AlejoBSmith/VentiladorMecanico/Imágenes/1_isometrico.PNG

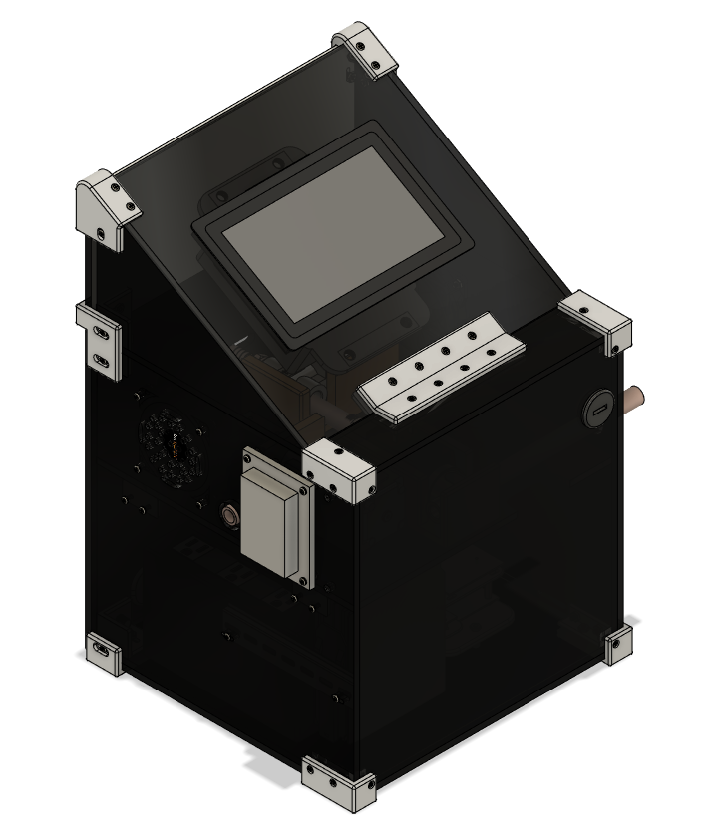
Imágenes/1_isometrico.PNG
