AlejoBSmith/VentiladorMecanico/Imágenes/4_isometrico.PNG

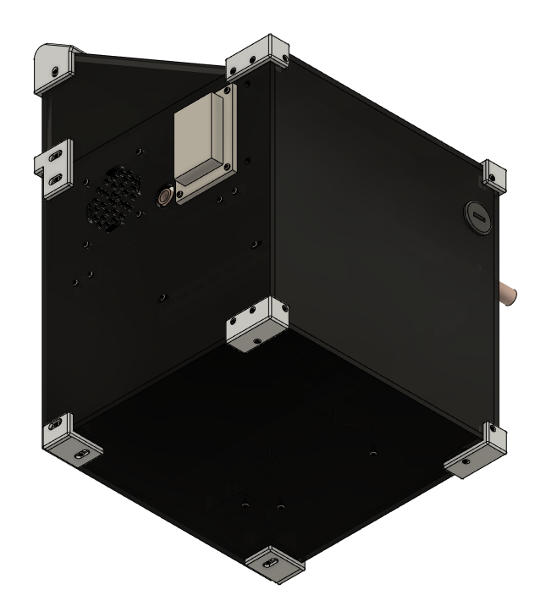
Imágenes/4_isometrico.PNG
