AlejoBSmith/VentiladorMecanico/Imágenes/5_isometrico.PNG

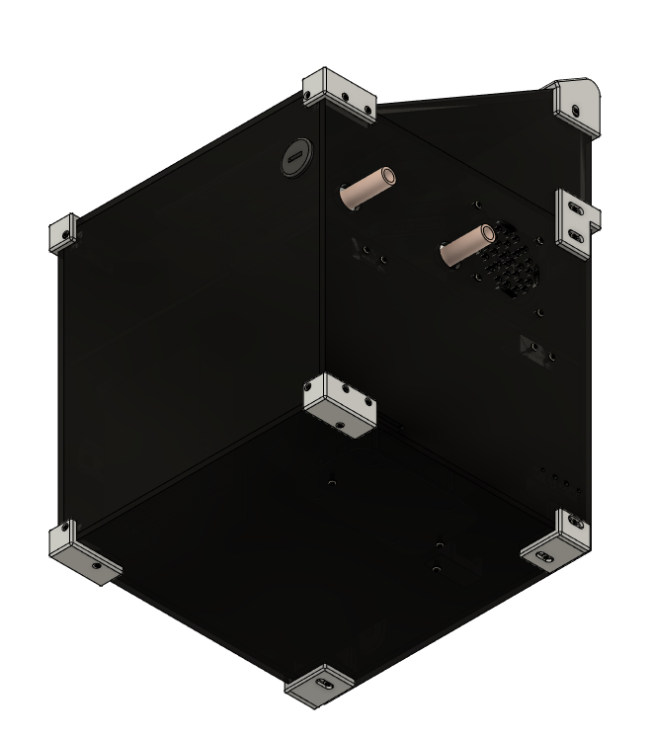
Imágenes/5_isometrico.PNG
