AlejoBSmith/VentiladorMecanico/Imágenes/7_isometrico.PNG

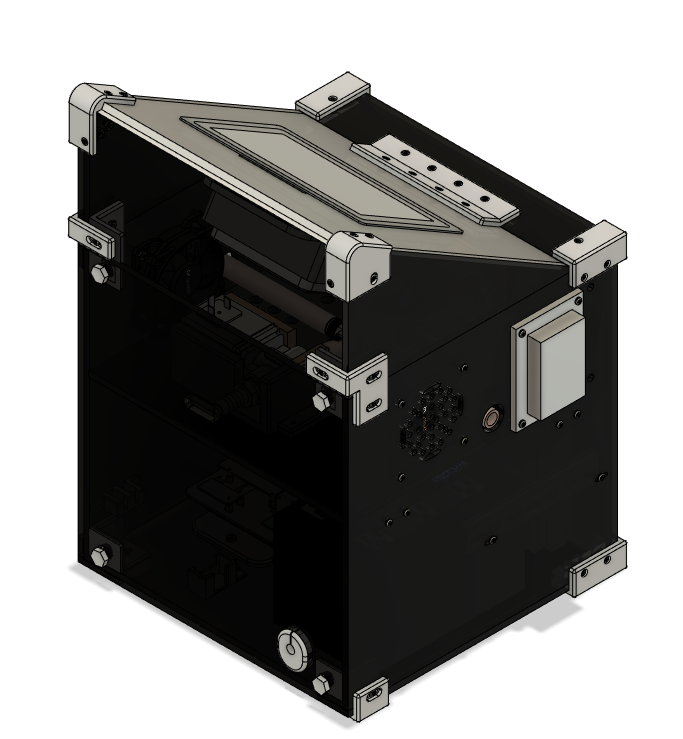
Imágenes/7_isometrico.PNG
