AlejoBSmith/VentiladorMecanico/Imágenes/8_isometrico.PNG

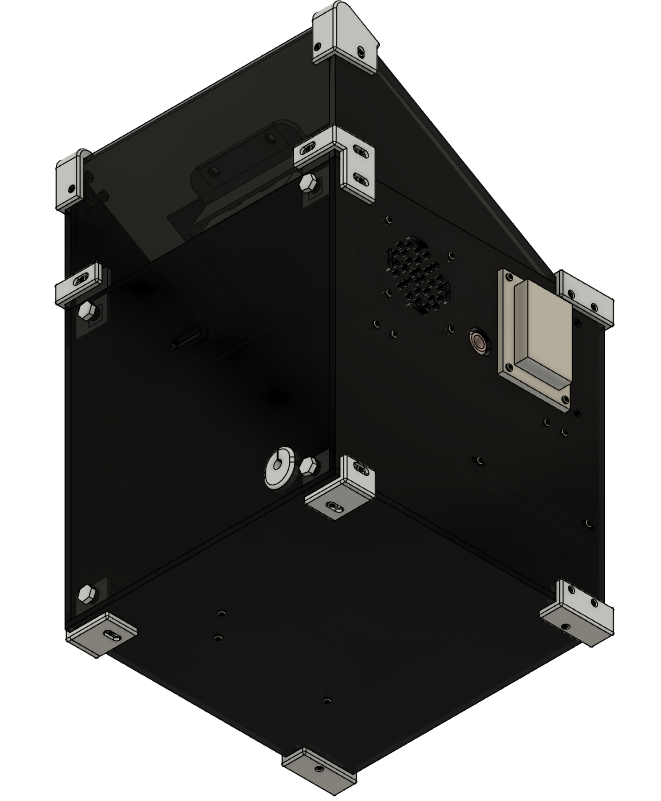
Imágenes/8_isometrico.PNG
