AlejoBSmith/VentiladorMecanico/Imágenes/9_isometrico.PNG

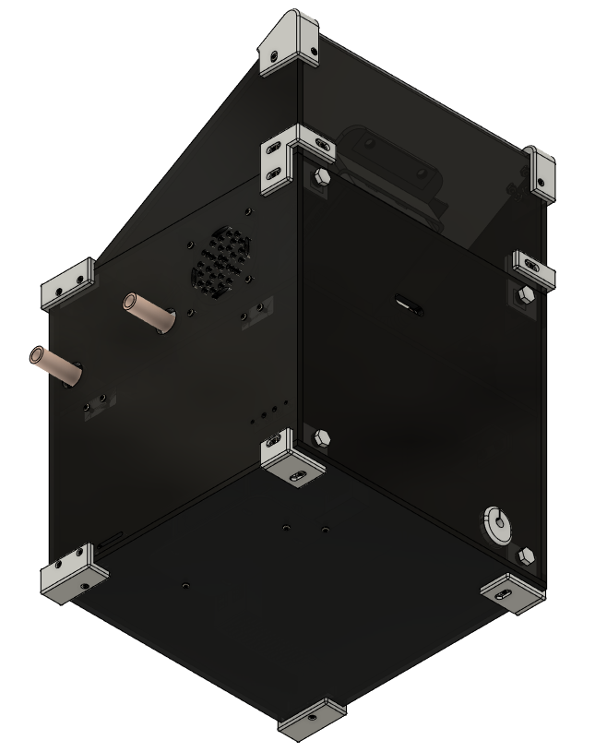
Imágenes/9_isometrico.PNG
