AlejoBSmith/VentiladorMecanico/Imágenes/10_frontal.PNG

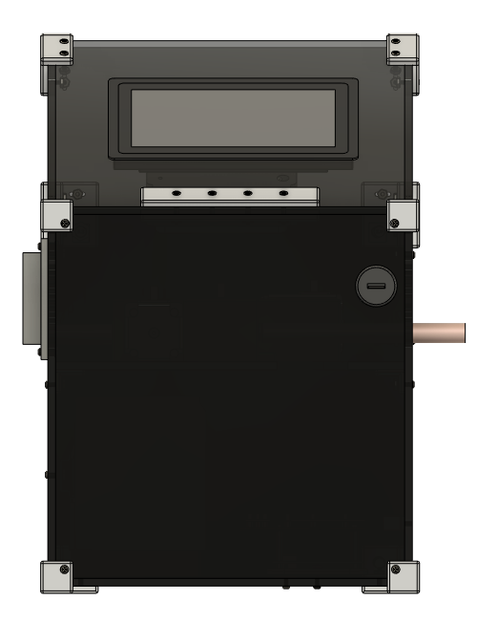
Imágenes/10_frontal.PNG
