AlejoBSmith/VentiladorMecanico/Imágenes/11_lateralderecho.PNG

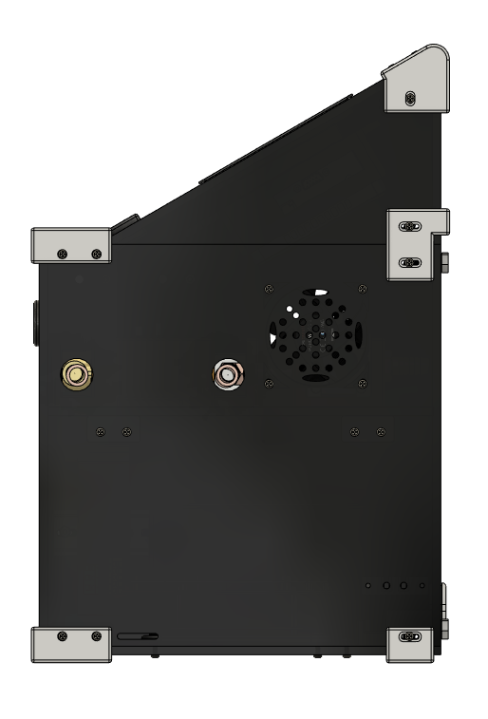
Imágenes/11_lateralderecho.PNG
