AlejoBSmith/VentiladorMecanico/Imágenes/12_inferior.PNG

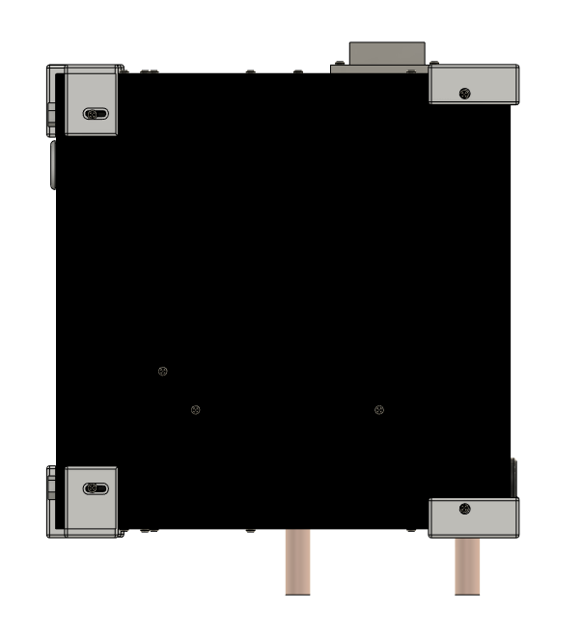
Imágenes/12_inferior.PNG
