AlejoBSmith/VentiladorMecanico/Imágenes/13_lateralizquierdo.PNG

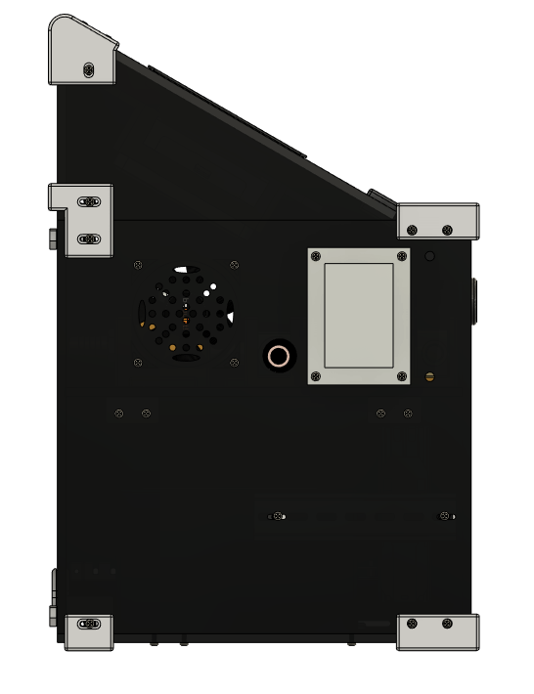
Imágenes/13_lateralizquierdo.PNG
