AlejoBSmith/VentiladorMecanico/Imágenes/14_trasero.PNG

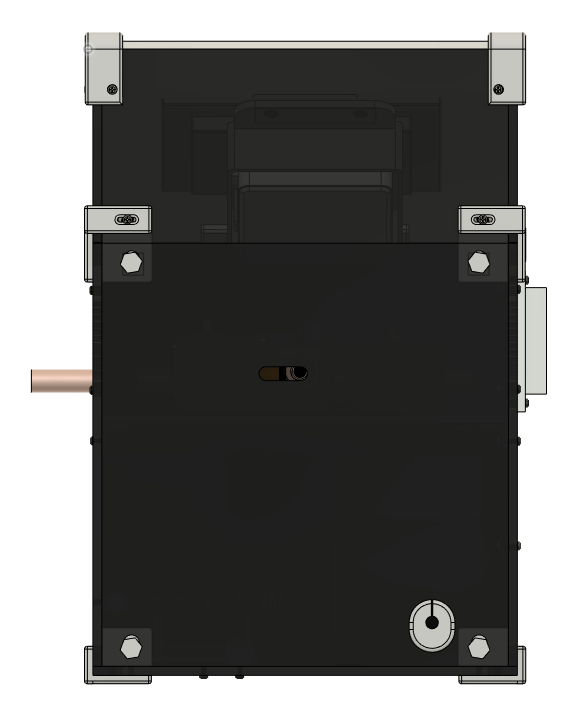
Imágenes/14_trasero.PNG
