AlejoBSmith/VentiladorMecanico/Imágenes/15_superior.PNG

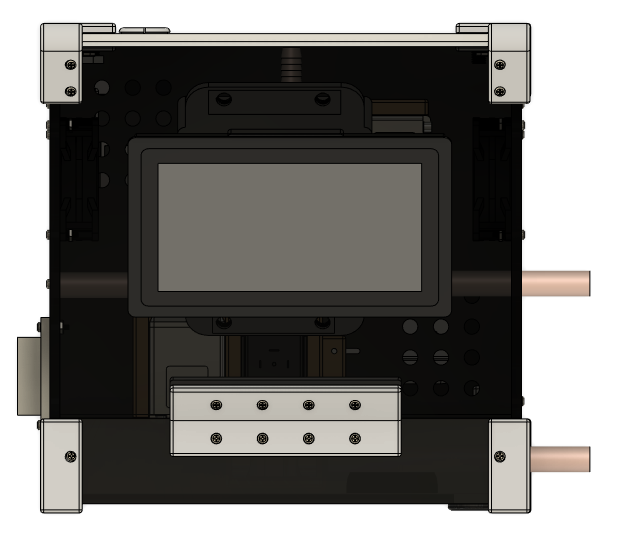
Imágenes/15_superior.PNG
