AlejoBSmith/VentiladorMecanico/Imágenes/18_neutmatica_Nivel1.PNG

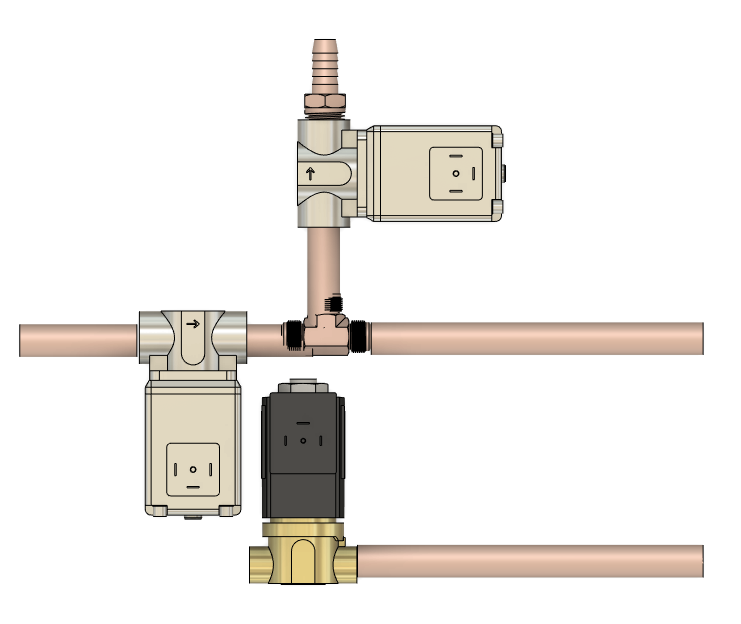
Imágenes/18_neutmatica_Nivel1.PNG
