AlejoBSmith/VentiladorMecanico/Impresión 3D/2_Inferiores/Nivel1.stl

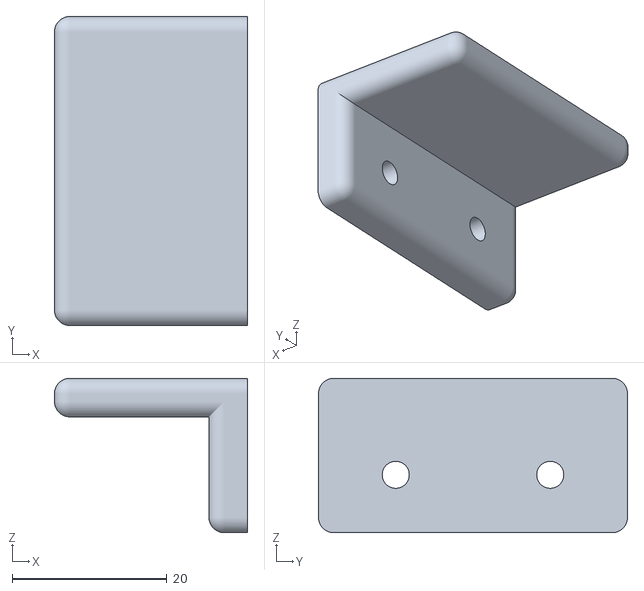
[picture p34: CAD file, 2021-11-26]
Impresión 3D/2_Inferiores/Nivel1.stl
25.0 x 40.0 x 20.0
