AlejoBSmith/VentiladorMecanico/Impresión 3D/3_Superiores/Tra_Izq_Ext_Sup_R.stl

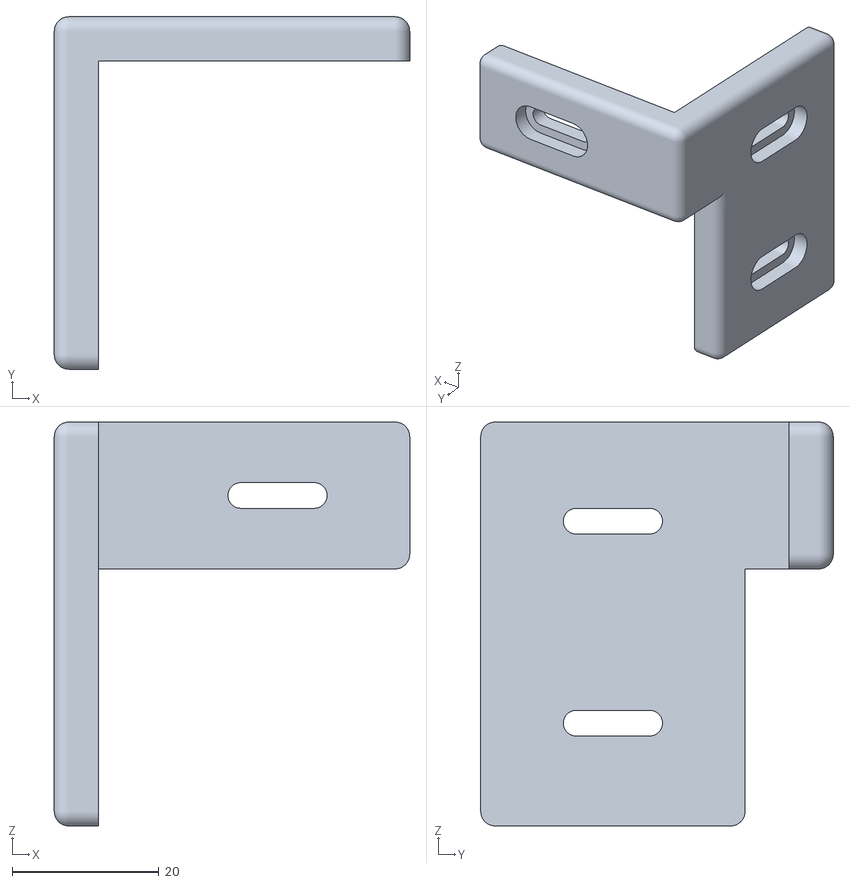
[picture p35: CAD file, 2021-11-26]
Impresión 3D/3_Superiores/Tra_Izq_Ext_Sup_R.stl
48.4 x 48.0 x 55.0
