AlejoBSmith/VentiladorMecanico/Cortadora Láser/paredFrontal.dxf

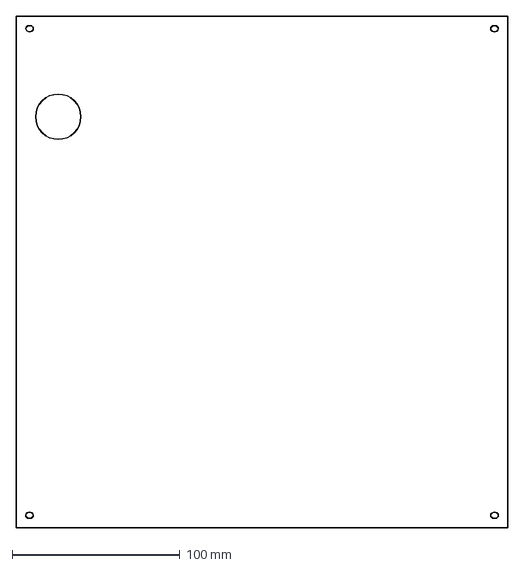
[picture p36: CAD file, 2021-11-26]
Cortadora Láser/paredFrontal.dxf
293.0 x 305.0 mm
