AlejoBSmith/VentiladorMecanico/Impresión 3D/3_Superiores/Sup_Izq_Int.stl

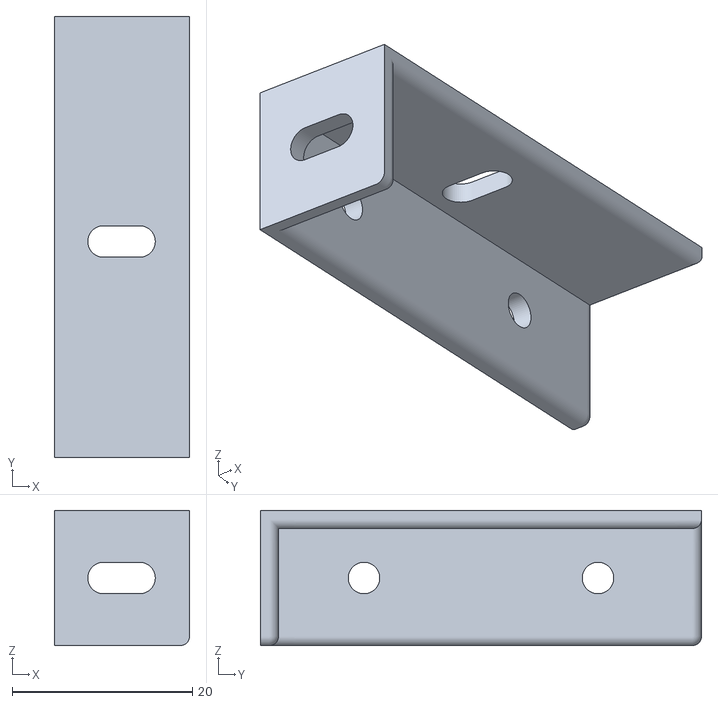
[picture p37: CAD file, 2021-11-26]
Impresión 3D/3_Superiores/Sup_Izq_Int.stl
15.0 x 49.0 x 15.0
