AlejoBSmith/VentiladorMecanico/Cortadora Láser/Nivel0.dxf

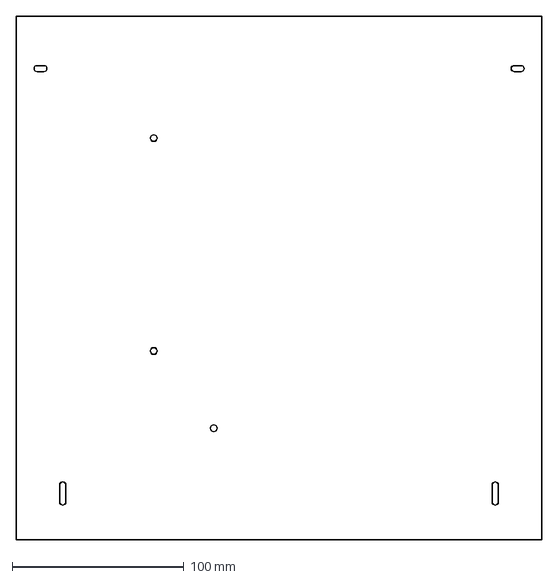
[picture p38: CAD file, 2021-11-26]
Cortadora Láser/Nivel0.dxf
306.0 x 305.0 mm
