AlejoBSmith/VentiladorMecanico/Impresión 3D/3_Superiores/Inclinado_Int.stl

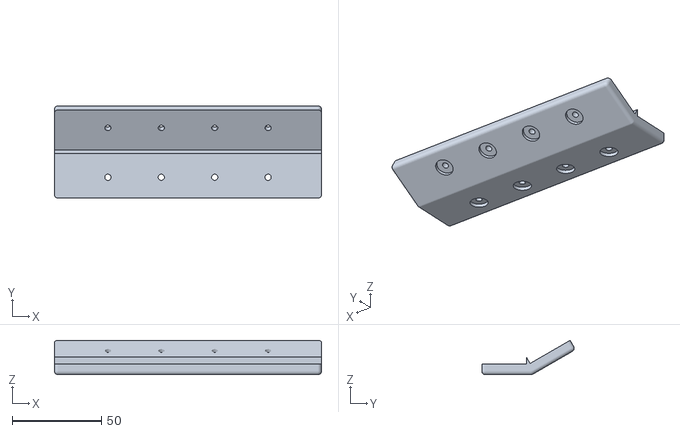
[picture p39: CAD file, 2021-11-26]
Impresión 3D/3_Superiores/Inclinado_Int.stl
150.0 x 51.9 x 19.3
