AlejoBSmith/VentiladorMecanico/Cortadora Láser/paredDerechoSup.dxf

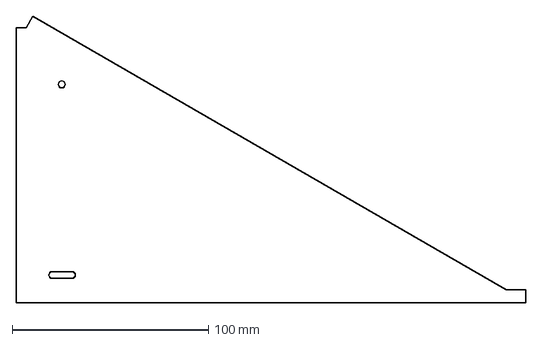
[picture p40: CAD file, 2021-11-26]
Cortadora Láser/paredDerechoSup.dxf
259.5 x 145.6 mm
